mymakercorner/the_manta75/images/IMG_20210131_110052.jpg

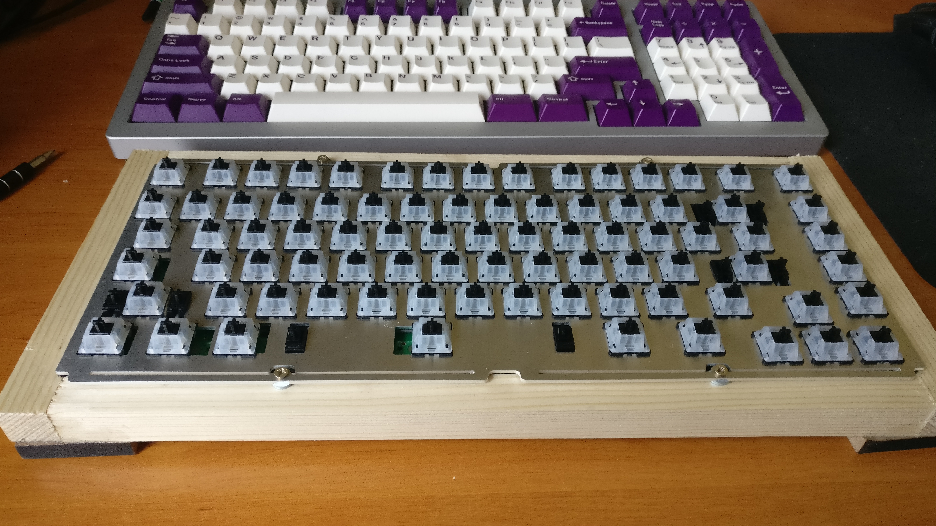
images/IMG_20210131_110052.jpg
